jatg81/HumTx/Board/Fotos/20181212_180108.jpg

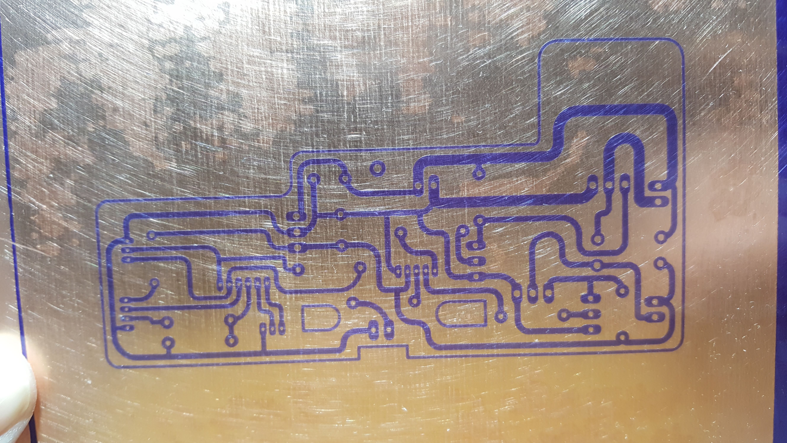
Board/Fotos/20181212_180108.jpg
