jatg81/HumTx/Board/Fotos/20181212_183240.jpg

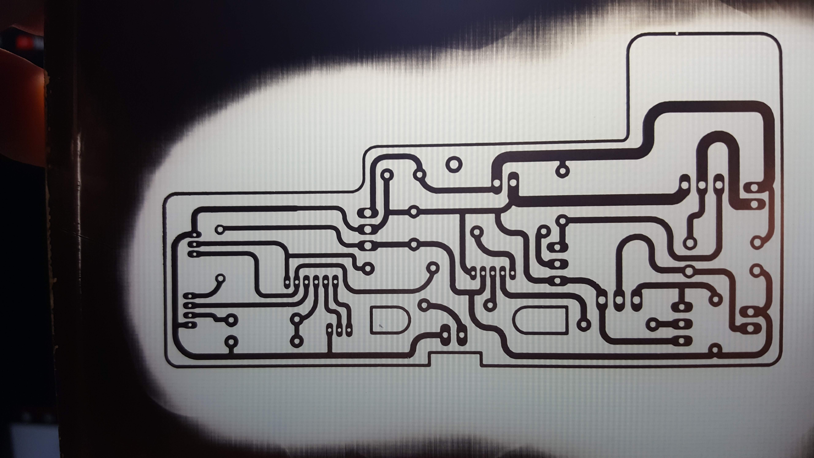
Board/Fotos/20181212_183240.jpg
