jatg81/HumTx/Board/Fotos/20181213_113239.jpg

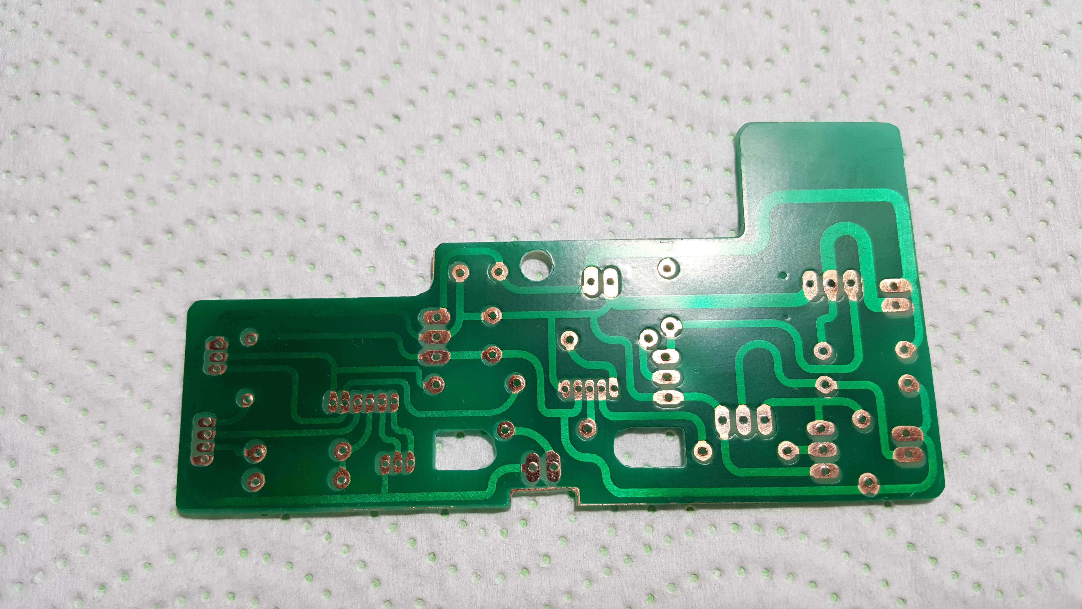
Board/Fotos/20181213_113239.jpg
