jatg81/HumTx/Board/Fotos/20181213_113309.jpg

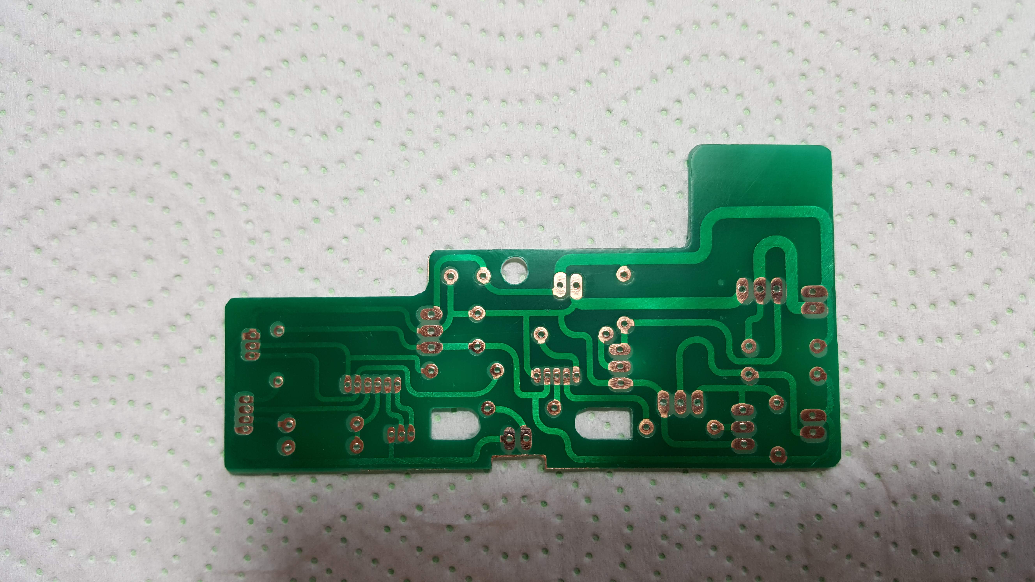
Board/Fotos/20181213_113309.jpg
