jatg81/HumTx/Board/Fotos/20181213_173636.jpg

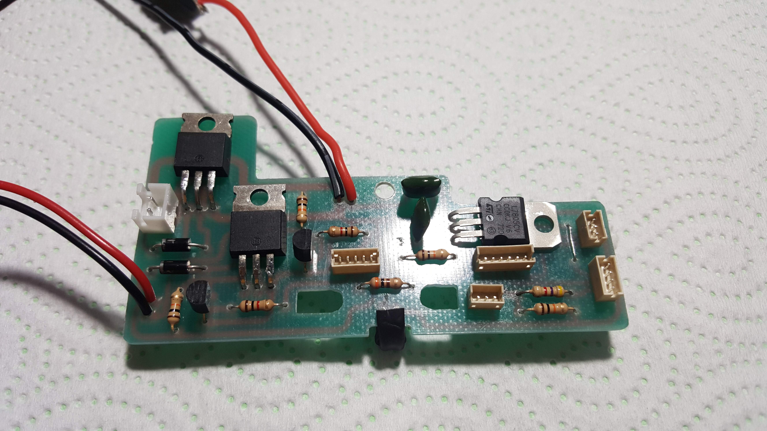
Board/Fotos/20181213_173636.jpg
