jatg81/HumTx/docs/test/20181207_154831.jpg

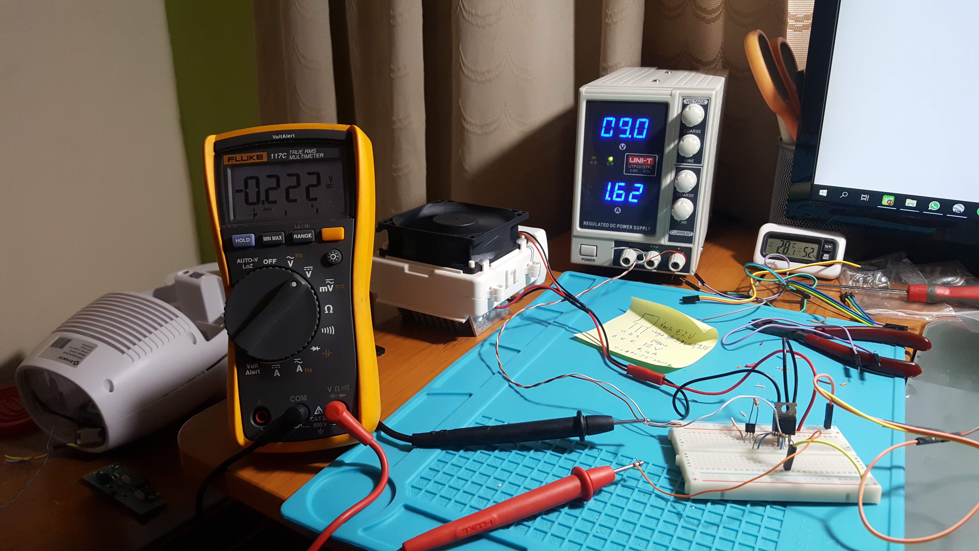
docs/test/20181207_154831.jpg
