jatg81/HumTx/docs/test/20181214_232352.jpg

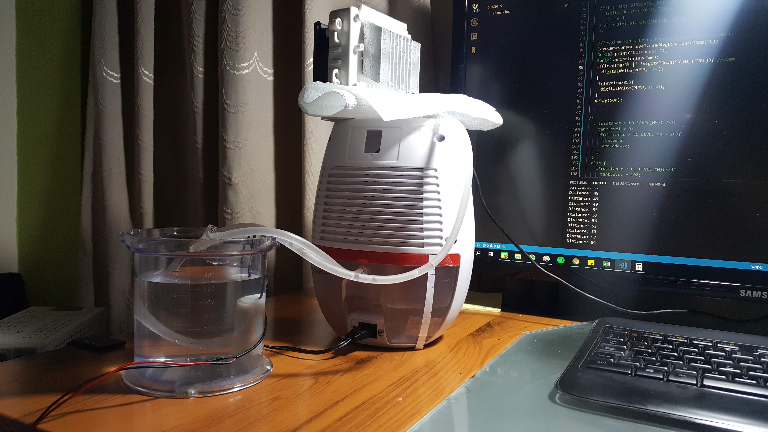
docs/test/20181214_232352.jpg
