jatg81/HumTx/docs/test/20181214_232401.jpg

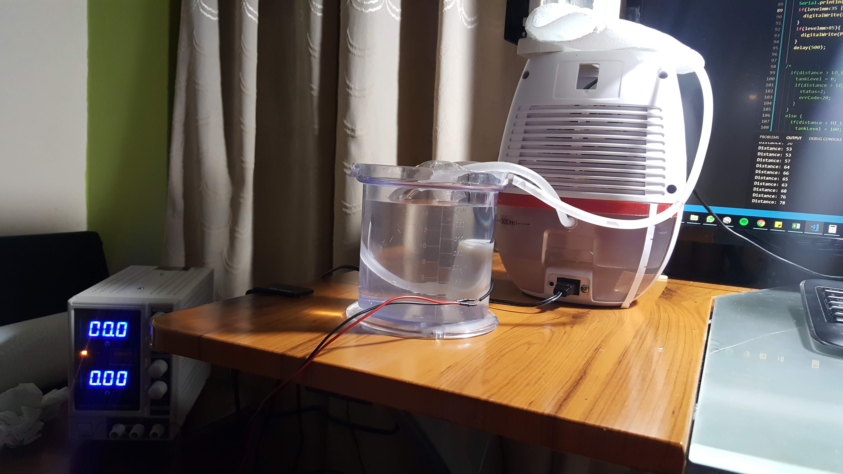
docs/test/20181214_232401.jpg
