jatg81/HumTx/docs/test/20181215_014937.jpg

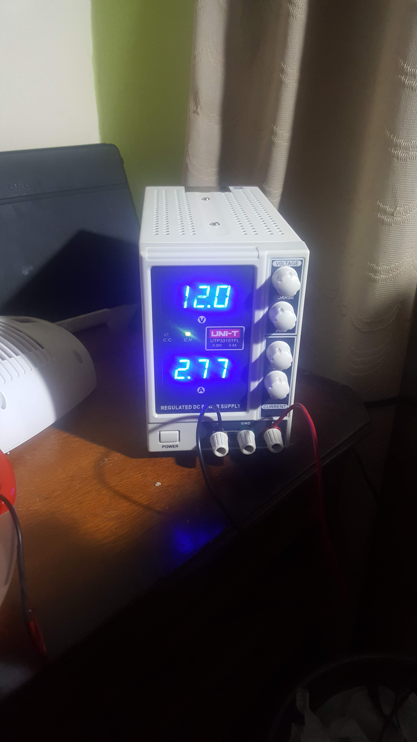
docs/test/20181215_014937.jpg
